wang-edward/ledaw/app/src/instrument.rs

//! Polyphonic synth with an owned `Osc -> Lpf -> Adsr` chain per voice.

pub mod juno;
pub mod sampler;

use raylib::prelude::*;

use crate::audio::{Context, Sample};
use crate::input::Event;
use crate::ui::Action;
use juno::{Juno, JunoUi};
use sampler::{Sampler, SamplerUi};

pub enum InstrumentKind {
    Juno,
    Sampler,
}

pub enum Instrument {
    Juno(Juno),
    Sampler(Sampler),
}

pub fn create(kind: InstrumentKind) -> (Instrument, InstrumentUi) {
    match kind {
        InstrumentKind::Juno => (
            Instrument::Juno(Juno::new()),
            InstrumentUi::Juno(JunoUi::new()),
        ),
        InstrumentKind::Sampler => (
            Instrument::Sampler(Sampler::default()),
            InstrumentUi::Sampler(SamplerUi::new()),
        ),
    }
}

impl Instrument {
    pub fn process(&mut self, ctx: &Context, out: &mut [Sample]) {
        match self {
            Instrument::Juno(x) => x.process(ctx, out),
            Instrument::Sampler(x) => x.process(ctx, out),
        }
    }

    pub fn note_on(&mut self, note: u8) {
        match self {
            Instrument::Juno(x) => x.note_on(note),
            Instrument::Sampler(x) => x.note_on(note),
        }
    }

    pub fn note_off(&mut self, note: u8) {
        match self {
            Instrument::Juno(x) => x.note_off(note),
            Instrument::Sampler(x) => x.note_off(note),
        }
    }

    pub fn all_notes_off(&mut self) {
        match self {
            Instrument::Juno(x) => x.all_notes_off(),
            Instrument::Sampler(x) => x.all_notes_off(),
        }
    }
}

pub enum InstrumentUi {
    Juno(JunoUi),
    Sampler(SamplerUi),
}

impl InstrumentUi {
    pub fn new(instrument: &Instrument) -> Self {
        match instrument {
            Instrument::Juno(_) => Self::Juno(JunoUi::new()),
            Instrument::Sampler(_) => Self::Sampler(SamplerUi::new()),
        }
    }

    pub fn matches(&self, instrument: &Instrument) -> bool {
        matches!(
            (self, instrument),
            (Self::Juno(_), Instrument::Juno(_)) | (Self::Sampler(_), Instrument::Sampler(_))
        )
    }

    pub fn handle_event(&mut self, instrument: &mut Instrument, event: Event) -> Action {
        match self {
            Self::Juno(ui) => {
                let Instrument::Juno(instrument) = instrument else {
                    debug_assert!(false, "Ui x Instrument mismatch");
                    return Action::None;
                };
                ui.handle_event(instrument, event)
            }
            Self::Sampler(ui) => {
                let Instrument::Sampler(instrument) = instrument else {
                    debug_assert!(false, "Ui x Instrument mismatch");
                    return Action::None;
                };
                ui.handle_event(instrument, event)
            }
        }
    }

    pub fn render<D: RaylibDraw>(&self, instrument: &Instrument, d: &mut D) {
        match self {
            Self::Juno(ui) => {
                let Instrument::Juno(instrument) = instrument else {
                    debug_assert!(false, "Ui x Instrument mismatch");
                    return;
                };
                ui.render(instrument, d);
            }
            Self::Sampler(ui) => {
                let Instrument::Sampler(instrument) = instrument else {
                    debug_assert!(false, "Ui x Instrument mismatch");
                    return;
                };
                ui.render(instrument, d);
            }
        }
    }
}
