wang-edward/ledaw/app/src/theme.rs

use raylib::prelude::*;

pub const COLOR1: Color = Color::new(0xf6, 0x51, 0x1d, 255);
pub const COLOR2: Color = Color::new(0xff, 0xb4, 0x00, 255);
pub const COLOR3: Color = Color::new(0x00, 0xa6, 0xed, 255);
pub const COLOR4: Color = Color::new(0x7f, 0xb8, 0x00, 255);
