wang-edward/ledaw/app/src/ui.rs

//! UI layer — ports the App/Timeline/Track/MidiEditor state machine and rendering from
//! `project.zig`. All audio state lives in the shared `Engine`; this layer holds only
//! UI/navigation state (mode, current screen, cursor/zoom, selection) plus the plugin
//! icon textures, and it locks the engine to read for rendering or to mutate on input.
//!
//! The Zig version returned `Op`s up a call stack to be queued onto the audio thread;
//! under the mutex model we mutate the engine directly while holding the lock.
//!
//! Feature-gated behind `ui`.

use std::collections::HashMap;
use std::sync::{Arc, Mutex};

use raylib::prelude::*;

use crate::engine::{Engine, MAX_PLUGINS, PLUGIN_LIST, PluginKind, PluginUi, TrackSource, create};
use crate::input::{Event, EventType, Key, Mods};
use crate::instrument::sampler::Sampler;
use crate::instrument::{Instrument, InstrumentUi};
use crate::interface::{HEIGHT, WIDTH, draw_text_centered};
use crate::midi::{self, frames_to_beats};

pub enum Action {
    None,
    GoBack,
}

#[derive(Clone, Copy, PartialEq, Eq)]
enum Mode {
    Normal,
    Insert,
}

#[derive(Clone, Copy)]
struct BeatFrame {
    center: f32,
    radius: f32,
}
impl BeatFrame {
    fn left(&self) -> f32 {
        self.center - self.radius
    }
    fn right(&self) -> f32 {
        self.center + self.radius
    }
    fn width(&self) -> f32 {
        self.radius * 2.0
    }
}

#[derive(Clone, Copy)]
struct BeatWindow {
    start: f32,
    len: f32,
}
impl BeatWindow {
    fn left(&self) -> f32 {
        self.start
    }
    fn right(&self) -> f32 {
        self.start + self.len
    }
}

pub struct Icons {
    map: HashMap<&'static str, Texture2D>,
}
impl Icons {
    /// Best-effort load; missing assets just render without an icon.
    pub fn load(rl: &mut RaylibHandle, thread: &RaylibThread) -> Self {
        let mut map = HashMap::new();
        if let Ok(t) = rl.load_texture(thread, "assets/water_spell.png") {
            map.insert("lpf", t);
        }
        if let Ok(t) = rl.load_texture(thread, "assets/slowed.png") {
            map.insert("delay", t);
        }
        Self { map }
    }
    fn get(&self, kind: PluginKind) -> Option<&Texture2D> {
        self.map.get(kind.name())
    }
}

pub struct App {
    engine: Arc<Mutex<Engine>>,
    icons: Icons,

    mode: Mode,
    note_offset: i16,
    active_notes: HashMap<Key, u8>,
    timeline: TimelineUi,
}

#[derive(Clone, Copy, PartialEq, Eq)]
enum TimelineScreen {
    Overview,
    MidiEditor,
    Track,
}

struct TimelineUi {
    screen: TimelineScreen,
    frame: BeatFrame,
    bar_width: f32,
    cursor: BeatWindow,
    step_size: f32,
    tracks: Vec<TrackUi>,
}

#[derive(Clone, Copy, PartialEq, Eq)]
enum TrackScreen {
    Overview,
    Plugin,
    PluginSelector,
    Instrument,
}

struct TrackUi {
    source: TrackSourceUi,
    screen: TrackScreen,
    active_plugin: usize,
    selector_index: usize,
    plugins: Vec<PluginUi>,
}

enum TrackSourceUi {
    Instrument(InstrumentUi),
    Audio,
}

impl TrackSourceUi {
    fn new(source: &TrackSource) -> Self {
        match source {
            TrackSource::Instrument { instrument, .. } => {
                Self::Instrument(InstrumentUi::new(instrument))
            }
            TrackSource::Audio { .. } => Self::Audio,
        }
    }

    fn matches(&self, source: &TrackSource) -> bool {
        match (self, source) {
            (Self::Instrument(ui), TrackSource::Instrument { instrument, .. }) => {
                ui.matches(instrument)
            }
            (Self::Audio, TrackSource::Audio { .. }) => true,
            _ => false,
        }
    }
}

const HEADER_HEIGHT: i32 = 12;
const ROW_HEIGHT: i32 = 28;

impl App {
    pub fn new(engine: Arc<Mutex<Engine>>, icons: Icons) -> Self {
        let tracks = engine
            .lock()
            .unwrap()
            .tracks()
            .iter()
            .map(|track| TrackUi::new(&track.source))
            .collect();
        Self {
            engine,
            icons,
            mode: Mode::Normal,
            note_offset: 0,
            active_notes: HashMap::new(),
            timeline: TimelineUi::new(tracks),
        }
    }

    pub fn handle_event(&mut self, ev: Event) {
        match self.mode {
            Mode::Insert => {
                if let Some(base) = midi::key_to_midi(ev.key) {
                    let raw = base as i16 + self.note_offset;
                    if !(0..=127).contains(&raw) {
                        return;
                    }
                    let note = raw as u8;
                    let mut eng = self.engine.lock().unwrap();
                    match ev.ty {
                        EventType::KeyPress => {
                            self.active_notes.insert(ev.key, note);
                            eng.note_on(note);
                        }
                        EventType::KeyRelease => {
                            if let Some(held) = self.active_notes.remove(&ev.key) {
                                eng.note_off(held);
                            }
                        }
                    }
                    return;
                }

                if ev.ty == EventType::KeyPress {
                    match ev.key {
                        Key::Escape => {
                            let mut eng = self.engine.lock().unwrap();
                            for (_, note) in self.active_notes.drain() {
                                eng.note_off(note);
                            }
                            self.mode = Mode::Normal;
                        }
                        Key::Z => self.note_offset = (self.note_offset - 12).max(-48),
                        Key::X => self.note_offset = (self.note_offset + 12).min(48),
                        _ => {}
                    }
                }
            }
            Mode::Normal => {
                if ev.ty != EventType::KeyPress {
                    return;
                }
                if ev.key == Key::I {
                    self.mode = Mode::Insert;
                    return;
                }
                let mut eng = self.engine.lock().unwrap();
                self.timeline.handle_event(ev, &mut eng);
            }
        }
    }

    pub fn render<D: RaylibDraw>(&mut self, d: &mut D) {
        let eng = self.engine.lock().unwrap();
        self.timeline.render(d, &eng, &self.icons);

        if self.mode == Mode::Insert {
            d.draw_rectangle_lines(0, 0, WIDTH, HEIGHT, Color::PURPLE);
        }
        if eng.recording {
            d.draw_rectangle_lines(1, 1, WIDTH - 2, HEIGHT - 2, Color::RED);
        }
    }
}

impl TimelineUi {
    fn new(tracks: Vec<TrackUi>) -> Self {
        Self {
            screen: TimelineScreen::Overview,
            frame: BeatFrame {
                center: 0.0,
                radius: 8.0,
            },
            bar_width: 4.0,
            cursor: BeatWindow {
                start: 0.0,
                len: 4.0,
            },
            step_size: 4.0,
            tracks,
        }
    }

    fn cursor_focus(&mut self) {
        if self.cursor.left() < self.frame.left() {
            self.frame.center -= self.frame.left() - self.cursor.left();
        } else if self.cursor.right() > self.frame.right() {
            self.frame.center += self.cursor.right() - self.frame.right();
        }
    }

    fn seek_to_cursor(&mut self, eng: &mut Engine) {
        eng.set_playhead(midi::beats_to_frames(
            self.cursor.left(),
            eng.bpm(),
            eng.sample_rate(),
        ));
        self.frame.center = self.cursor.left();
    }

    fn cursor_to_playhead(&mut self, eng: &Engine) {
        let beat = frames_to_beats(eng.timeline.playhead, eng.bpm(), eng.sample_rate());
        self.cursor.start = (beat / self.bar_width).floor() * self.bar_width;
        self.frame.center = beat;
        self.cursor_focus();
    }

    fn handle_event(&mut self, ev: Event, eng: &mut Engine) {
        match self.screen {
            TimelineScreen::Overview => match (ev.key, ev.mods) {
                (Key::Enter, _) => self.screen = TimelineScreen::Track,
                (Key::E, _) => self.screen = TimelineScreen::MidiEditor,
                (Key::H, _) if !eng.playing && !eng.recording => {
                    self.cursor.start = (self.cursor.start - self.step_size).max(0.0);
                    self.cursor_focus();
                }
                (Key::L, _) if !eng.playing && !eng.recording => {
                    self.cursor.start += self.step_size;
                    self.cursor_focus();
                }
                (Key::J, _) if !eng.recording => {
                    let at = eng.timeline.active_track;
                    if at + 1 < eng.track_count() {
                        eng.set_active_track(at + 1);
                    }
                }
                (Key::K, _) if !eng.recording => {
                    let at = eng.timeline.active_track;
                    if at > 0 {
                        eng.set_active_track(at - 1);
                    }
                }
                (Key::Space, _) => {
                    if eng.playing {
                        eng.toggle_play();
                        self.cursor_to_playhead(eng);
                    } else {
                        self.seek_to_cursor(eng);
                        eng.toggle_play();
                    }
                }
                (Key::Backspace, _) if !eng.playing && !eng.recording => {
                    self.cursor.start = 0.0;
                    self.cursor_focus();
                }
                (Key::R, _) => {
                    if eng.recording {
                        eng.toggle_record();
                        self.cursor_to_playhead(eng);
                    } else {
                        self.seek_to_cursor(eng);
                        eng.toggle_record();
                    }
                }
                (Key::O, Mods::None) if eng.track_count() < crate::engine::MAX_TRACKS => {
                    let track = crate::engine::Track::new(TrackSource::Instrument {
                        instrument: Instrument::Sampler(Sampler::default()),
                        notes: Vec::new(),
                    });
                    let track_ui = TrackUi::new(&track.source);
                    if eng.add_track(track) {
                        self.tracks.push(track_ui);
                    }
                }
                (Key::O, Mods::Shift) if eng.track_count() < crate::engine::MAX_TRACKS => {
                    let track = crate::engine::Track::new(TrackSource::Audio { clips: Vec::new() });
                    let track_ui = TrackUi::new(&track.source);
                    if eng.add_track(track) {
                        self.tracks.push(track_ui);
                    }
                }
                (Key::Minus, _) if eng.track_count() > 1 => {
                    let at = eng.timeline.active_track;
                    if eng.remove_track(at) {
                        self.tracks.remove(at);
                    }
                }
                (Key::RightBracket, _) => self.frame.radius = (self.frame.radius / 2.0).max(2.0),
                (Key::LeftBracket, _) => self.frame.radius = (self.frame.radius * 2.0).min(128.0),
                _ => {}
            },
            TimelineScreen::MidiEditor => {
                if ev.key == Key::Backspace {
                    self.screen = TimelineScreen::Overview;
                }
            }
            TimelineScreen::Track => {
                let at = eng.timeline.active_track;
                if self.tracks[at].handle_event(ev, eng, at) {
                    self.screen = TimelineScreen::Overview;
                }
            }
        }
    }

    fn render<D: RaylibDraw>(&mut self, d: &mut D, eng: &Engine, icons: &Icons) {
        debug_assert_eq!(self.tracks.len(), eng.track_count());
        match self.screen {
            TimelineScreen::Overview => {
                d.draw_text("TIMELINE_OVERVIEW", 30, 30, 10, Color::LIGHTGRAY);
                let w = WIDTH as f32;
                let num_rows = eng.track_count().min(crate::engine::MAX_TRACKS);
                let b = frames_to_beats(eng.timeline.playhead, eng.bpm(), eng.sample_rate());

                if eng.playing {
                    self.frame.center = b;
                }

                let position = if eng.playing { b } else { self.cursor.left() };
                let bar = (position / self.bar_width).floor() as i32;
                let beat_in_bar = (position % self.bar_width) as i32;
                let label = format!("{}.{}", bar + 1, beat_in_bar + 1);
                draw_text_centered(d, &label, WIDTH / 2, HEADER_HEIGHT / 2, 8, Color::WHITE);

                let mut bar_pos = (self.frame.left() / self.bar_width).floor() * self.bar_width;
                while bar_pos < self.frame.right() {
                    let pct = (bar_pos - self.frame.left()) / self.frame.width();
                    let x = (pct * w) as i32;
                    d.draw_line(
                        x,
                        HEADER_HEIGHT,
                        x,
                        HEADER_HEIGHT + num_rows as i32 * ROW_HEIGHT,
                        Color::DARKGRAY,
                    );
                    bar_pos += self.bar_width;
                }

                for i in 0..num_rows {
                    let row_y = i as i32 * ROW_HEIGHT + HEADER_HEIGHT;
                    d.draw_rectangle_lines(0, row_y, WIDTH, ROW_HEIGHT, Color::DARKGRAY);
                    match &eng.track(i).source {
                        TrackSource::Instrument { notes, .. } => {
                            for note in notes {
                                let sb = frames_to_beats(note.start, eng.bpm(), eng.sample_rate());
                                let eb = frames_to_beats(note.end, eng.bpm(), eng.sample_rate());
                                if eb < self.frame.left() || sb > self.frame.right() {
                                    continue;
                                }
                                let lp = (sb - self.frame.left()) / self.frame.width();
                                let rp = (eb - self.frame.left()) / self.frame.width();
                                let x1 = (lp * w).max(0.0) as i32;
                                let x2 = (rp * w).min(w) as i32;
                                let slot = 23 - (note.note % 24) as i32;
                                let ny = row_y + 2 + slot;
                                d.draw_line(x1, ny, x2.max(x1 + 1), ny, Color::GREEN);
                            }
                        }
                        TrackSource::Audio { clips } => {
                            for clip in clips {
                                if clip.audio.samples.is_empty() || clip.audio.sample_rate <= 0.0 {
                                    continue;
                                }

                                let clip_frames = (clip.audio.samples.len() as f32
                                    * eng.sample_rate()
                                    / clip.audio.sample_rate)
                                    as u64;
                                let start =
                                    frames_to_beats(clip.start, eng.bpm(), eng.sample_rate());
                                let end = frames_to_beats(
                                    clip.start + clip_frames,
                                    eng.bpm(),
                                    eng.sample_rate(),
                                );
                                if end < self.frame.left() || start > self.frame.right() {
                                    continue;
                                }

                                let x1 = (((start - self.frame.left()) / self.frame.width()
                                    * WIDTH as f32)
                                    .max(0.0)) as i32;
                                let x2 = (((end - self.frame.left()) / self.frame.width()
                                    * WIDTH as f32)
                                    .min(WIDTH as f32))
                                    as i32;
                                let x2 = x2.max(x1 + 1);
                                let center = row_y + ROW_HEIGHT / 2;
                                let amplitude = ROW_HEIGHT / 2 - 3;

                                d.draw_rectangle(
                                    x1,
                                    row_y + 1,
                                    x2 - x1,
                                    ROW_HEIGHT - 1,
                                    Color::new(0, 82, 172, 128),
                                );
                                let samples_per_pixel = self.frame.width() * 60.0 / eng.bpm()
                                    * clip.audio.sample_rate
                                    / WIDTH as f32;

                                for x in x1..x2 {
                                    let beat = self.frame.left()
                                        + x as f32 / WIDTH as f32 * self.frame.width();

                                    let frame =
                                        midi::beats_to_frames(beat, eng.bpm(), eng.sample_rate());

                                    let start_idx = ((frame.saturating_sub(clip.start) as f32)
                                        * clip.audio.sample_rate
                                        / eng.sample_rate())
                                        as usize;

                                    let end_idx = (start_idx as f32 + samples_per_pixel) as usize;

                                    let start_idx = start_idx.min(clip.audio.samples.len() - 1);
                                    let end_idx =
                                        end_idx.max(start_idx + 1).min(clip.audio.samples.len());

                                    let (min, max) = clip.audio.samples[start_idx..end_idx]
                                        .iter()
                                        .fold((0.0f32, 0.0f32), |(min, max), sample| {
                                            (min.min(*sample), max.max(*sample))
                                        });

                                    let top = center - (max * amplitude as f32) as i32;
                                    let bottom = center - (min * amplitude as f32) as i32;

                                    d.draw_line(x, top, x, bottom, Color::WHITE);
                                }
                            }
                        }
                    }
                }

                let row = eng.timeline.active_track as i32;
                let y = row * ROW_HEIGHT + HEADER_HEIGHT;
                d.draw_rectangle_lines(0, y, WIDTH, ROW_HEIGHT, Color::RED);

                if self.frame.left() < b && b < self.frame.right() {
                    let pct = (b - self.frame.left()) / self.frame.width();
                    let x = (pct * w) as i32;
                    d.draw_line(x, HEADER_HEIGHT, x, HEIGHT, Color::WHITE);
                }

                if !eng.playing && !eng.recording {
                    let lp = (self.cursor.left() - self.frame.left()) / self.frame.width();
                    let rp = (self.cursor.right() - self.frame.left()) / self.frame.width();
                    let lx = (lp * w) as i32;
                    let rx = (rp * w) as i32;
                    d.draw_rectangle_lines(lx, y, rx - lx, ROW_HEIGHT, Color::ORANGE);
                }
            }
            TimelineScreen::MidiEditor => {
                d.draw_text("MIDI_EDITOR", 30, 30, 10, Color::LIGHTGRAY);
            }
            TimelineScreen::Track => {
                let at = eng.timeline.active_track;
                self.tracks[at].render(d, eng, icons, at);
            }
        }
    }
}

impl TrackUi {
    fn new(source: &TrackSource) -> Self {
        Self {
            source: TrackSourceUi::new(source),
            screen: TrackScreen::Overview,
            active_plugin: 0,
            selector_index: 0,
            plugins: Vec::new(),
        }
    }

    fn handle_event(&mut self, ev: Event, eng: &mut Engine, track_idx: usize) -> bool {
        debug_assert!(self.source.matches(&eng.track(track_idx).source));
        debug_assert_eq!(self.plugins.len(), eng.track(track_idx).plugins.len());
        match self.screen {
            TrackScreen::Overview => {
                let plugin_count = eng.track(track_idx).plugins.len();
                match ev.key {
                    Key::Backspace => return true,
                    Key::A => self.screen = TrackScreen::PluginSelector,
                    Key::S => self.screen = TrackScreen::Instrument,
                    Key::Enter if plugin_count > 0 => self.screen = TrackScreen::Plugin,
                    Key::H if self.active_plugin > 0 => self.active_plugin -= 1,
                    Key::L if plugin_count > 0 => {
                        self.active_plugin = (self.active_plugin + 1).min(plugin_count - 1);
                    }
                    _ => {}
                }
            }
            TrackScreen::Plugin => {
                if self.plugins.get(self.active_plugin).is_none() {
                    return false;
                }
                let Some(plugin) = eng.track_mut(track_idx).plugins.get_mut(self.active_plugin)
                else {
                    return false;
                };
                let Some(ui) = self.plugins.get_mut(self.active_plugin) else {
                    return false;
                };
                if let Action::GoBack = ui.handle_event(plugin, ev) {
                    self.screen = TrackScreen::Overview;
                }
            }
            TrackScreen::PluginSelector => match ev.key {
                Key::Backspace => self.screen = TrackScreen::Overview,
                Key::K if self.selector_index > 0 => self.selector_index -= 1,
                Key::J if self.selector_index + 1 < PLUGIN_LIST.len() => {
                    self.selector_index += 1;
                }
                Key::Enter => {
                    let (plugin, ui) = create(PLUGIN_LIST[self.selector_index]);
                    if eng.add_plugin(track_idx, plugin) {
                        self.plugins.push(ui);
                        self.screen = TrackScreen::Overview;
                    }
                }
                _ => {}
            },
            TrackScreen::Instrument => {
                let (TrackSourceUi::Instrument(ui), TrackSource::Instrument { instrument, .. }) =
                    (&mut self.source, &mut eng.track_mut(track_idx).source)
                else {
                    self.screen = TrackScreen::Overview;
                    return false;
                };
                if let Action::GoBack = ui.handle_event(instrument, ev) {
                    self.screen = TrackScreen::Overview;
                }
            }
        }
        false
    }

    fn render<D: RaylibDraw>(&self, d: &mut D, eng: &Engine, icons: &Icons, track_idx: usize) {
        debug_assert!(self.source.matches(&eng.track(track_idx).source));
        debug_assert_eq!(self.plugins.len(), eng.track(track_idx).plugins.len());
        match self.screen {
            TrackScreen::Overview => {
                let track = eng.track(track_idx);
                d.draw_rectangle(0, 0, 32, 32, Color::RED);
                draw_text_centered(d, &track_idx.to_string(), 16, 16, 8, Color::LIGHTGRAY);

                for i in 0..5 {
                    d.draw_line(i * 32, 64, i * 32, 128, Color::WHITE);
                }
                for i in 0..3 {
                    d.draw_line(0, 64 + i * 32, 128, 64 + i * 32, Color::WHITE);
                }

                for i in 0..track.plugins.len() {
                    let x = (i as i32 % 4) * 32 + 16;
                    let y = (i as i32 / 4) * 32 + 64 + 16;
                    let kind = track.plugins[i].kind();
                    if let Some(tex) = icons.get(kind) {
                        d.draw_texture(tex, x - 8, y - 8, Color::WHITE);
                    }
                    let name = kind.name();
                    let tw = crate::interface::measure_text(name, 10);
                    d.draw_text(name, x - tw / 2, y + 6, 10, Color::WHITE);
                    if i == self.active_plugin {
                        d.draw_circle(x, y, 5.0, Color::GREEN);
                    }
                }
                for i in track.plugins.len()..MAX_PLUGINS {
                    let x = (i as i32 % 4) * 32 + 16;
                    let y = (i as i32 / 4) * 32 + 64 + 16;
                    d.draw_circle(x, y, 1.0, Color::RED);
                    d.draw_text("none", x - 11, y + 4, 10, Color::WHITE);
                }

                d.draw_text("TRACK", 30, 30, 10, Color::LIGHTGRAY);
            }
            TrackScreen::Plugin => {
                let track = eng.track(track_idx);
                if self.plugins.get(self.active_plugin).is_none() {
                    return;
                }
                let Some(plugin) = track.plugins.get(self.active_plugin) else {
                    return;
                };
                let Some(ui) = self.plugins.get(self.active_plugin) else {
                    return;
                };
                ui.render(plugin, d);
            }
            TrackScreen::PluginSelector => {
                for (i, tag) in PLUGIN_LIST.iter().enumerate() {
                    let y = i as i32 * 16;
                    let color = if i == self.selector_index {
                        Color::RED
                    } else {
                        Color::BLUE
                    };
                    d.draw_rectangle(0, y, 128, 16, Color::DARKGRAY);
                    d.draw_text(tag.name(), 0, y, 5, color);
                }
            }
            TrackScreen::Instrument => {
                let (TrackSourceUi::Instrument(ui), TrackSource::Instrument { instrument, .. }) =
                    (&self.source, &eng.track(track_idx).source)
                else {
                    return;
                };
                ui.render(instrument, d);
            }
        }
    }
}
